coniferconifer/ESP32-A2DP-surround/surroundAMP.kicad_sch

## KiCad design surroundAMP.kicad_sch (2024-07-20)

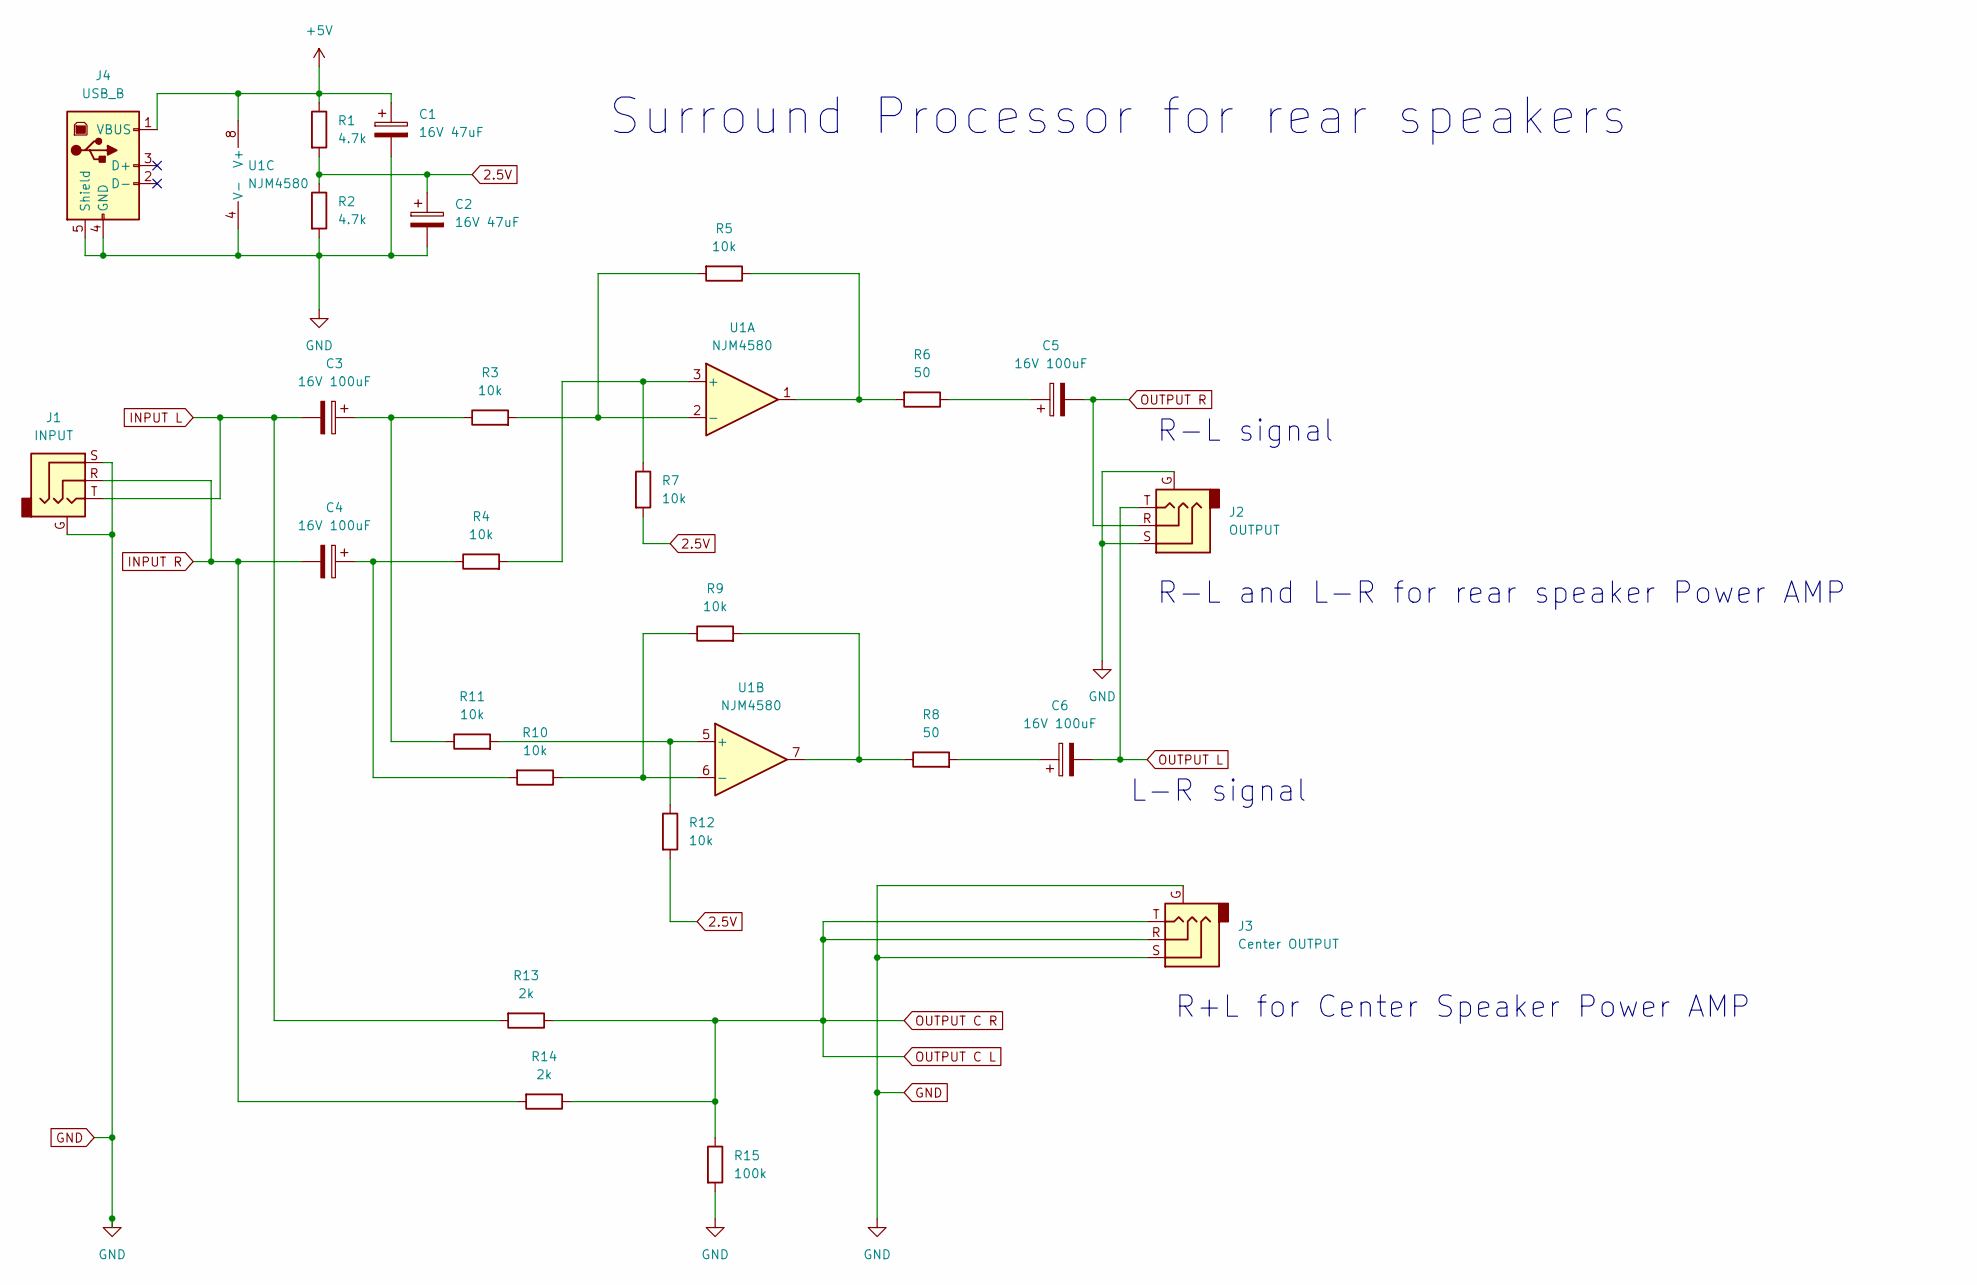
[picture p7: schematic surroundAMP.kicad_sch]

Parts:
C1, C2: 16V 47uF
C3, C4, C5, C6: 16V 100uF
J1: INPUT
J2: OUTPUT
J3: Center OUTPUT
J4: USB_B
R1, R2: 4.7k
R3, R4, R5, R7, R9, R10, R11, R12: 10k
R6, R8: 50
R13, R14: 2k
R15: 100k
U1: NJM4580

Connections:
2.5V: C2.1, R1.2, R2.1, R7.2, R12.2
+5V: C1.1, J4.1 (VBUS), R1.1, U1.8 (V+)
GND: C1.2, C2.2, J1.G, J1.S, J2.G, J2.S, J3.G, J3.S, J4.4 (GND), J4.5 (Shield), R2.2, R15.2, U1.4 (V-)
INPUT L: C3.2, J1.T, R13.2
INPUT R: C4.2, J1.R, R14.2
unnamed: C3.1, R3.1, R11.1
unnamed: C4.1, R4.1, R10.2
unnamed: C5.1, R6.1
unnamed: C6.1, R8.2
unnamed: R3.2, R5.2, U1.2 (-)
unnamed: R4.2, R7.1, U1.3 (+)
unnamed: R5.1, R6.2, U1.1
unnamed: R8.1, R9.2, U1.7
unnamed: R9.1, R10.1, U1.6 (-)
unnamed: R11.2, R12.1, U1.5 (+)
OUTPUT C L: J3.R, J3.T, R13.1, R14.1, R15.1
OUTPUT L: C6.2, J2.T
OUTPUT R: C5.2, J2.R

Notes on the sheet:
R-L and L-R for rear speaker Power AMP
R+L for Center Speaker Power AMP
L-R signal
Surround Processor for rear speakers
R-L signal
